Goga64/ULK/Gallery/169pcb.jpg

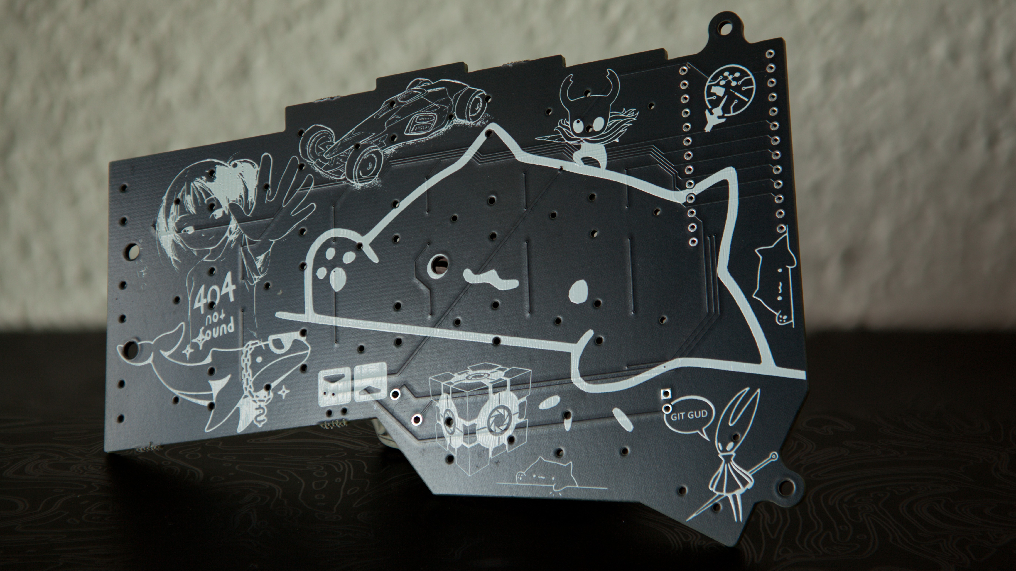
Gallery/169pcb.jpg
