Goga64/ULK/Gallery/169white.jpg

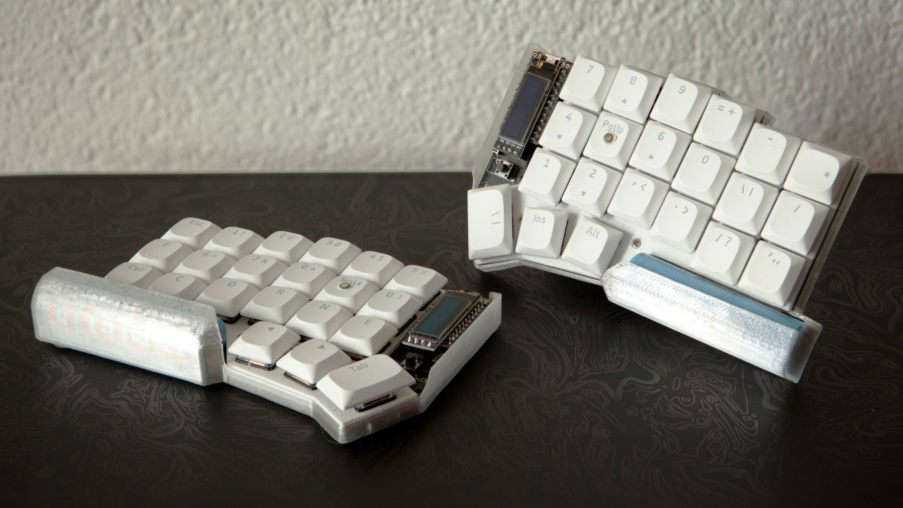
Gallery/169white.jpg
