Goga64/ULK/Gallery/another_contrast_map.png

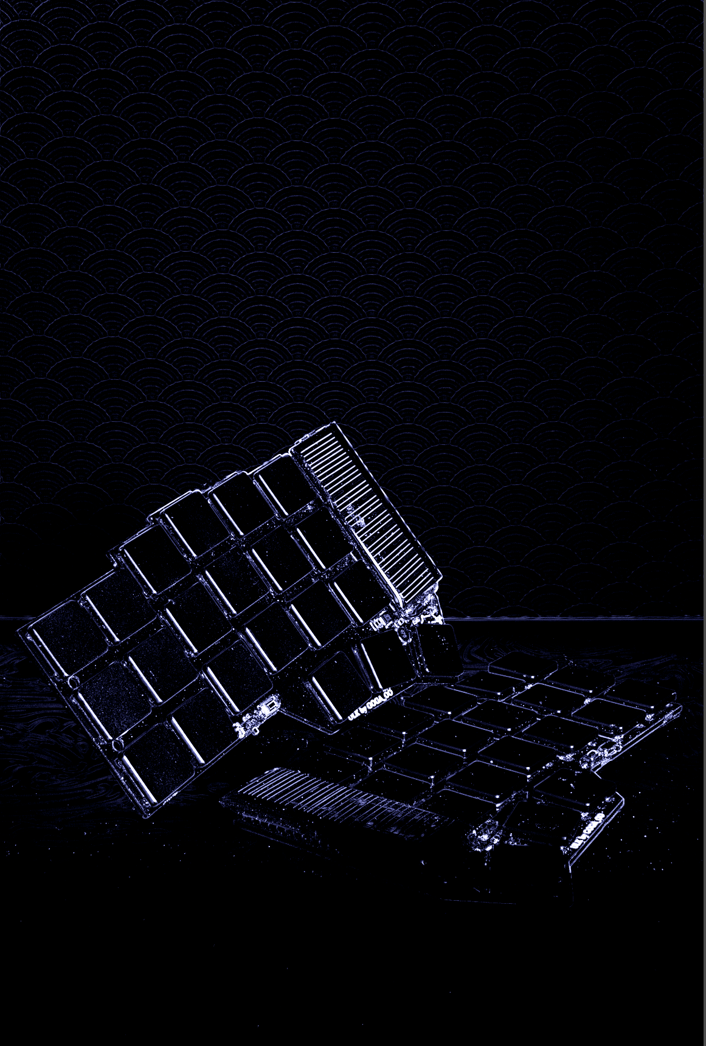
Gallery/another_contrast_map.png
