Goga64/ULK/Gallery/funcky_contrast_map.png

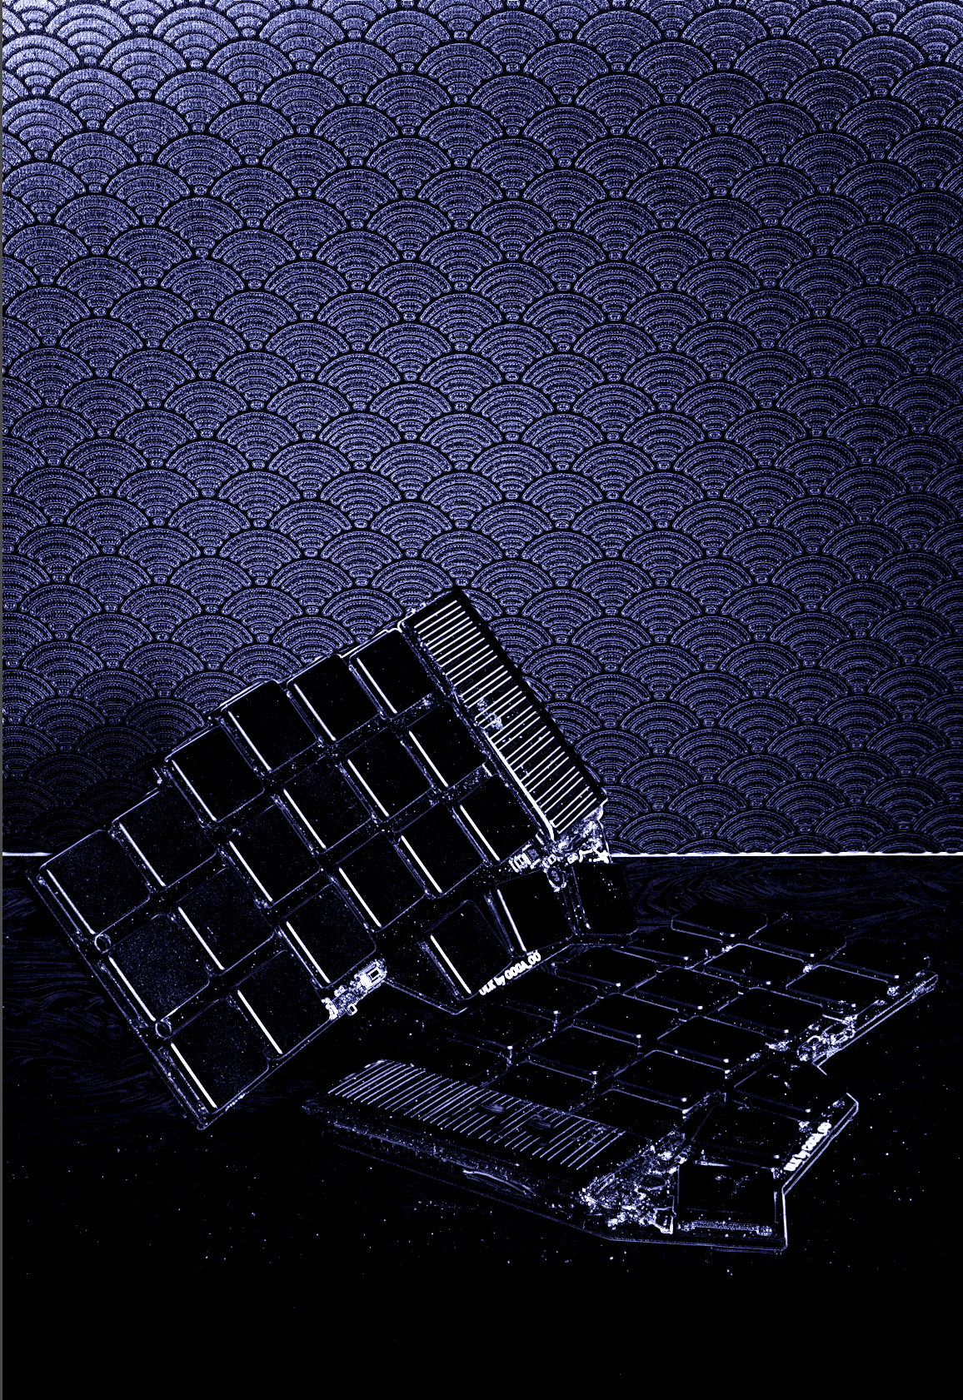
Gallery/funcky_contrast_map.png
