Goga64/ULK/KiCad/ULK_sl_PG1316s/ULK v7.png

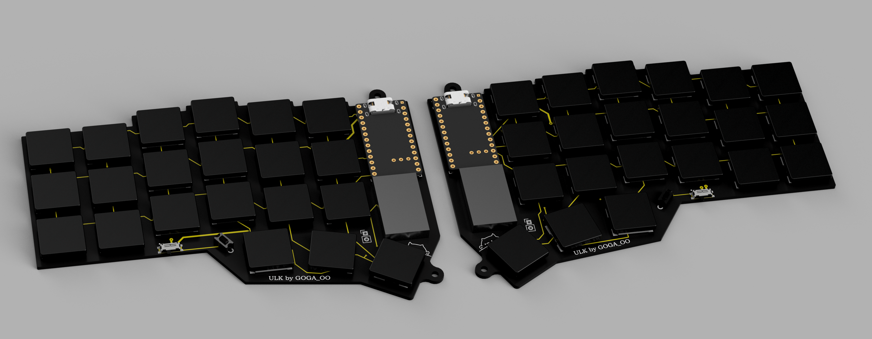
KiCad/ULK_sl_PG1316s/ULK v7.png
